YuWei-CH/RedSun_Clock/supplementary material/MAX7219 Example.png

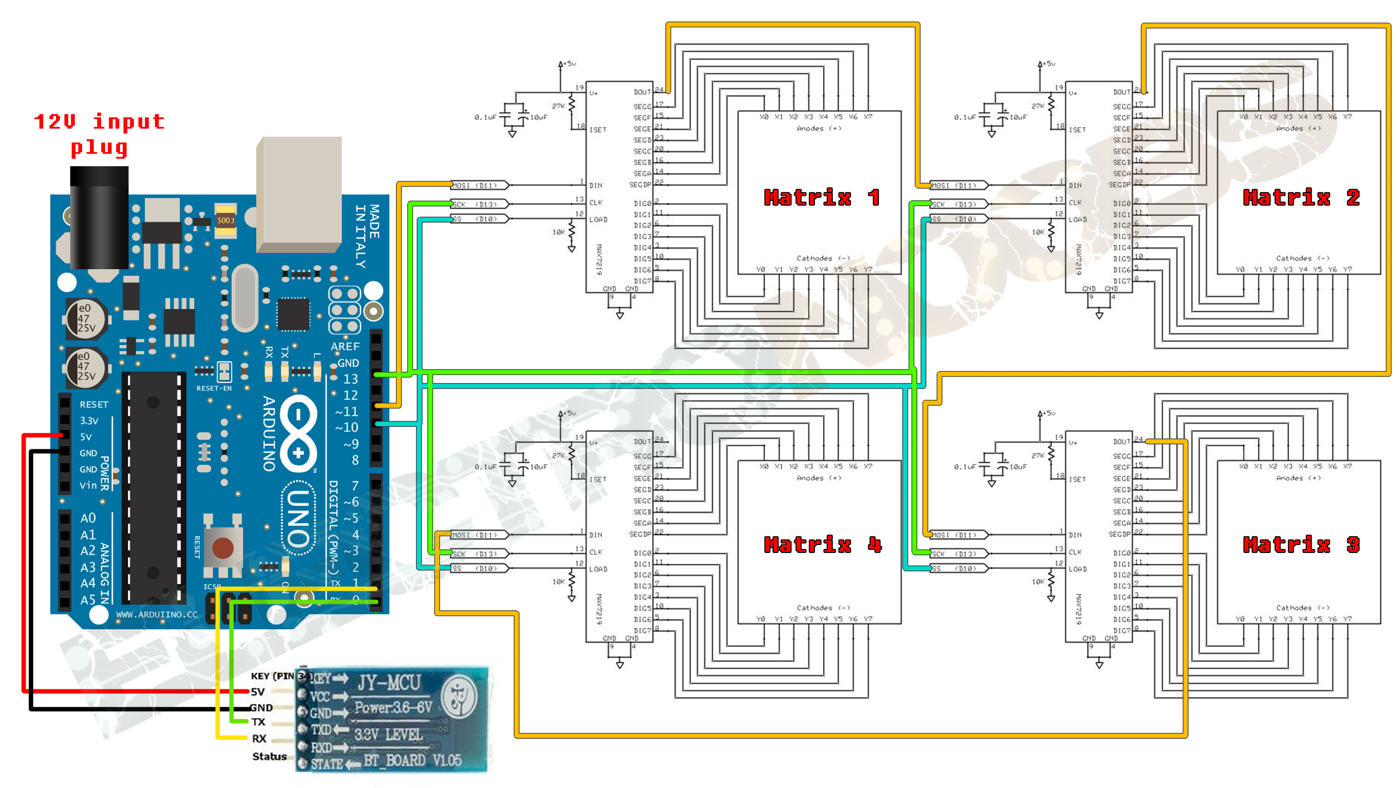
supplementary material/MAX7219 Example.png
