YuWei-CH/RedSun_Clock/supplementary material/prototype1.pic.jpg

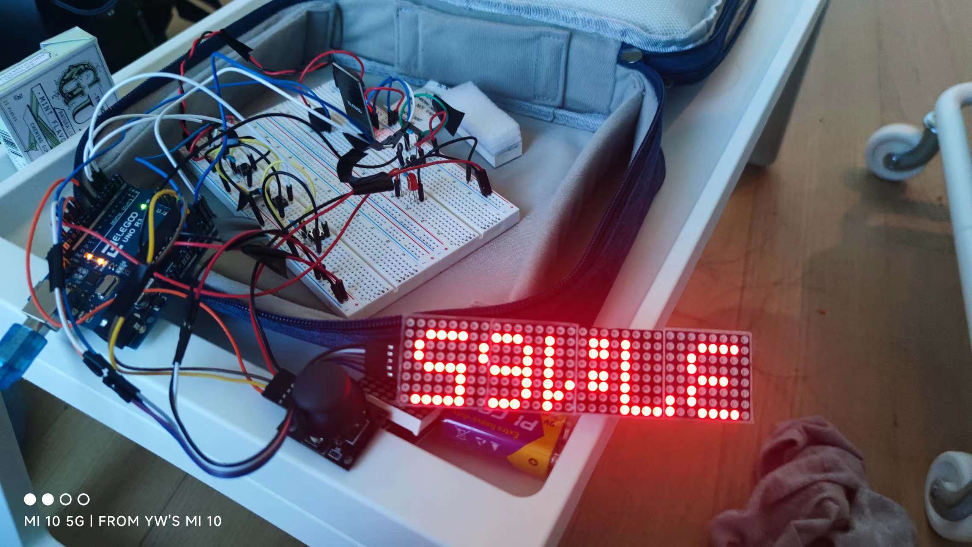
supplementary material/prototype1.pic.jpg
