YuWei-CH/RedSun_Clock/supplementary material/prototype2.pic.jpg

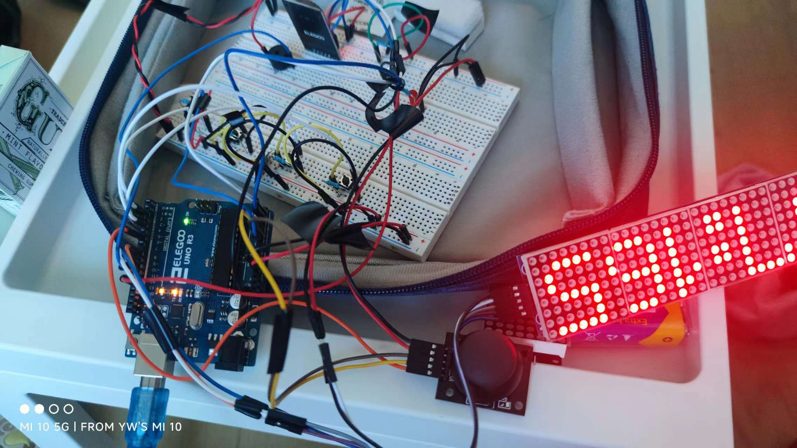
supplementary material/prototype2.pic.jpg
