YuWei-CH/RedSun_Clock/supplementary material/prototype3.pic.jpg

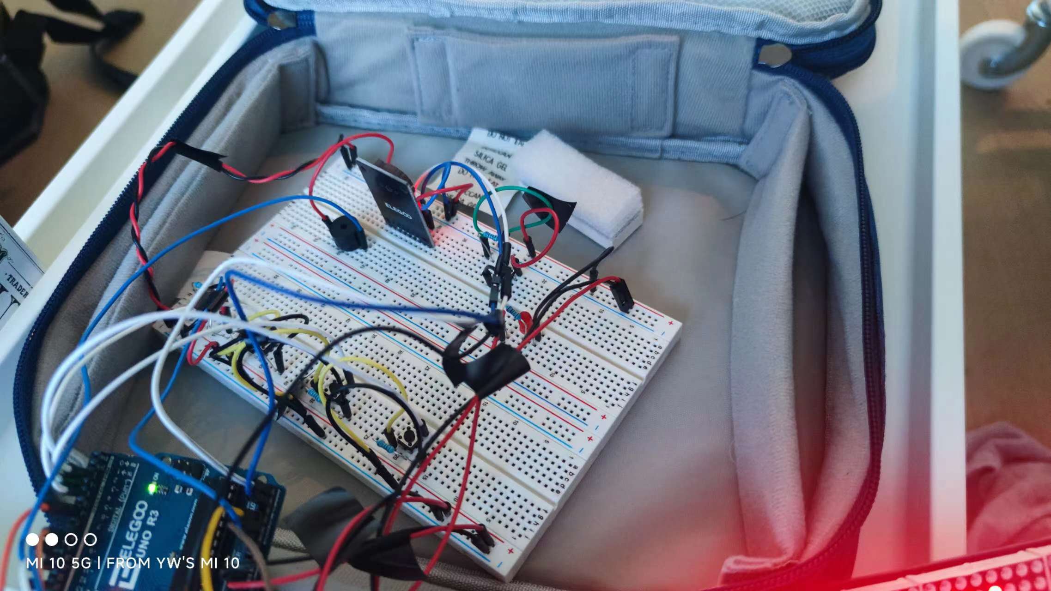
supplementary material/prototype3.pic.jpg
