YuWei-CH/RedSun_Clock/Code/Sample_Arduino/Joystick_controll/Joystick_controll.ino

int VRx = A1;
int VRy = A2;
int SW = 6;

int xPosition = 0;
int yPosition = 0;
int SW_state = 0;
int mapX = 0;
int mapY = 0;

// Y : < -400 UP; 0 - 50 stay; > 400 down
   X : > 400 Left; 0 - 50 stay; < -400 right
   SW: 0 push;

void setup() {
  Serial.begin(9600); 
  
  pinMode(VRx, INPUT);
  pinMode(VRy, INPUT);
  pinMode(SW, INPUT_PULLUP); 
  
}

void loop() {
  xPosition = analogRead(VRx);
  yPosition = analogRead(VRy);
  SW_state = digitalRead(SW);
  mapX = map(xPosition, 0, 1023, -512, 512);
  mapY = map(yPosition, 0, 1023, -512, 512);
  
  Serial.print("X: ");
  Serial.print(mapX);
  Serial.print(" | Y: ");
  Serial.print(mapY);
  Serial.print(" | Button: ");
  Serial.println(SW_state);

  delay(1000);
  
}
