YuWei-CH/RedSun_Clock/Code/Sample_Arduino/Dot_matrix_display/Dot_display/Dot_display.ino

//Mario's Ideas
//MAX7219 - using Led Control library to display all leds one by one
#include <LedControl.h>

int DIN = 10;
int CS =8;
int CLK = 9;

LedControl lc=LedControl(DIN, CLK, CS,0);



void setup() {

  lc.shutdown(0,false);
  lc.setIntensity(0,0);
  lc.clearDisplay(0);
}

void loop() {
lc.setLed(0,0,0,true);
display_1();
  
//  for(int j=0;j<8;j++){
//     for(int i=0;i<8;i++){
//       lc.setLed(0,j,i,true);
//       delay(100);
//       lc.setLed(0,j,i,false);
//     }
//  }
}


void display_1(){
  for (int i = 0; i < 8; ++i){
  lc.setLed(0,i,3,true);
  lc.setLed(0,i,12,true);
}
delay (1000);
 for (int i = 0; i < 8; ++i){
  lc.setLed(0,i,3,false);
  lc.setLed(0,i,12,false);
}
delay (500);
}
